RrPt/REM/Gehaeuse/REM-M/REM-M-Unterteil_V2.0.stl

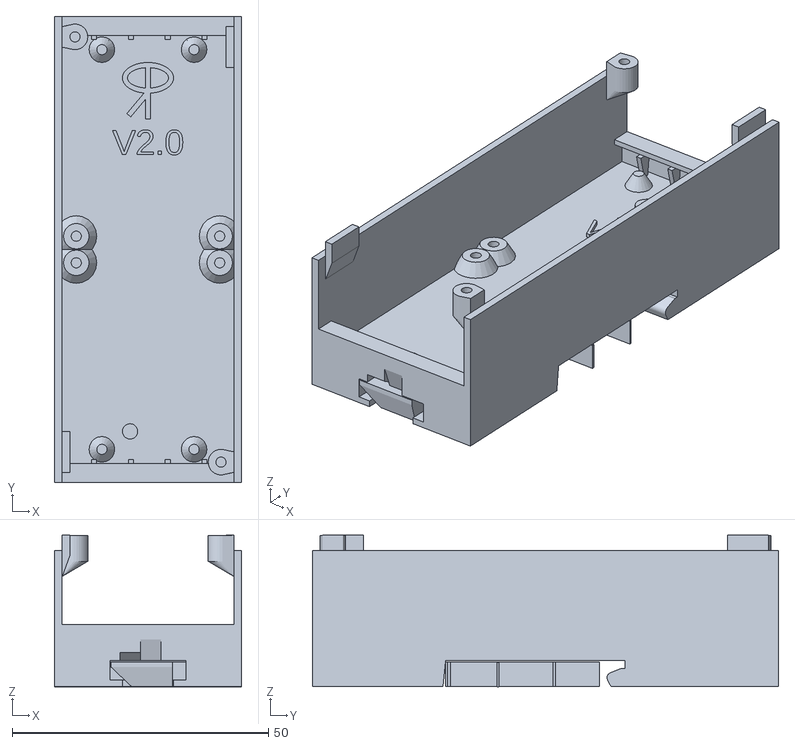
[picture p20: CAD file, 2020-09-23]
Gehaeuse/REM-M/REM-M-Unterteil_V2.0.stl
36.5 x 91.0 x 29.6
