RrPt/REM/REM-Platinen/3d/Lolin32.FCStd

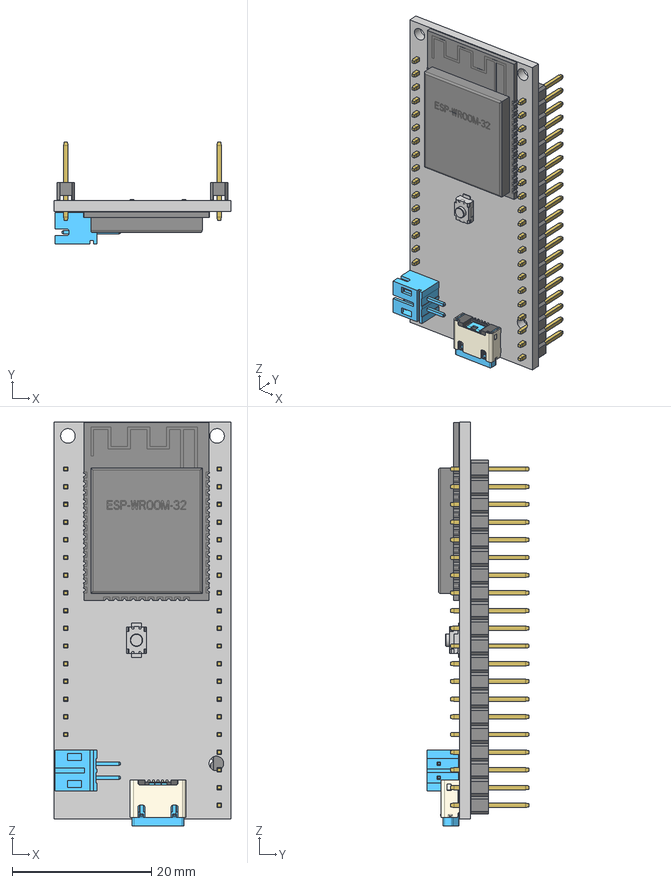
[picture p21: CAD file, 2020-09-23]
REM-Platinen/3d/Lolin32.FCStd
25.4 x 14.6 x 58.0 mm
W\X\FCrth 629105150521 Micro USB (Housing)
W\X\FCrth 629105150521 Micro USB (Inner Shield)
W\X\FCrth 629105150521 Micro USB (Outer Shield)
W\X\FCrth 629105150521 Micro USB ( Contact 1,2,4,5)
W\X\FCrth 629105150521 Micro USB ( Contact 1,2,4,5)001
W\X\FCrth 629105150521 Micro USB ( Contact 1,2,4,5)002
W\X\FCrth 629105150521 Micro USB ( Contact 1,2,4,5)003
W\X\FCrth 629105150521 Micro USB ( Contact 3)
B2B-PH-K-S v1
BASE, 2
PIN, 2
PIN, 003
PIN, 004
PIN, 005
PIN, 006
PIN, 007
PIN, 008
PIN, 009
PIN, 010
PIN, 011
PIN, 012
PIN, 013
PIN, 014
PIN, 015
PIN, 016
PIN, 017
BASE, 003
PIN, 018
PIN, 019
PIN, 020
PIN, 021
PIN, 022
PIN, 023
PIN, 024
PIN, 025
PIN, 026
PIN, 027
PIN, 028
PIN, 029
PIN, 030
PIN, 031
PIN, 032
PIN, 033
ESP-WROOM-32
3x4x2 tact button v1
BASE, 004
PIN, 039
PIN, 036
PIN, 041
PIN, 042
PIN, 038
PIN, 037
PIN, 047
PIN, 043
PIN, 048
PIN, 044
PIN, 040
PIN, 045
PIN, 046
PIN, 049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
