RrPt/REM/REM-Platinen/Platinen/modules/3dpackages/LED_D3.0mm_long.step

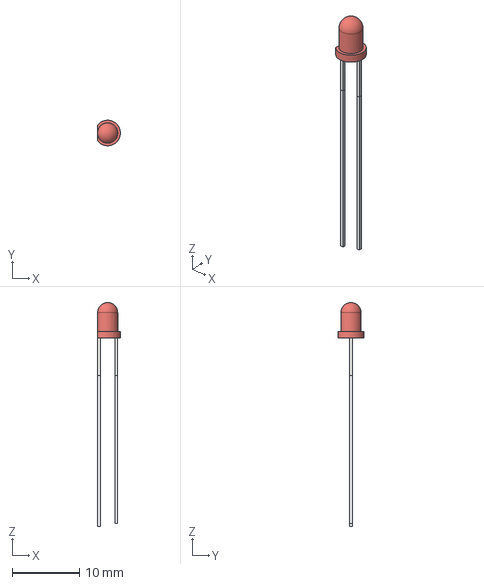
[picture p22: CAD file, 2020-09-23]
REM-Platinen/Platinen/modules/3dpackages/LED_D3.0mm_long.step
3.40 x 3.80 x 33.2 mm
