RrPt/REM/Gehaeuse/REM-M/REM-M-Klammer_V1.2.stl

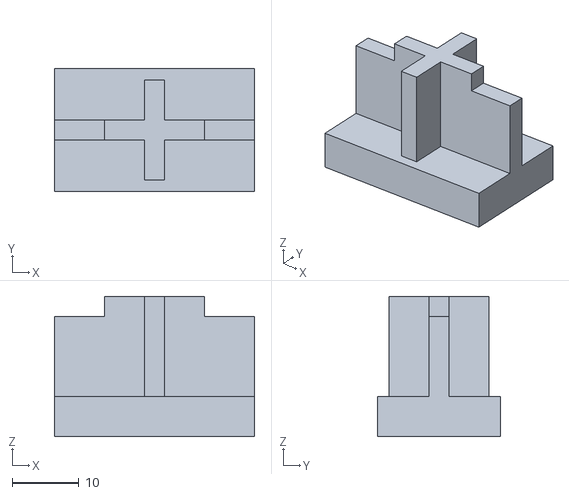
[picture p23: CAD file, 2020-09-23]
Gehaeuse/REM-M/REM-M-Klammer_V1.2.stl
30.0 x 18.5 x 21.0
