RrPt/REM/REM-Platinen/Platinen/modules/3dpackages/PinHeader_2x05_P2.54mm_Vertical_mit_Stecker.step

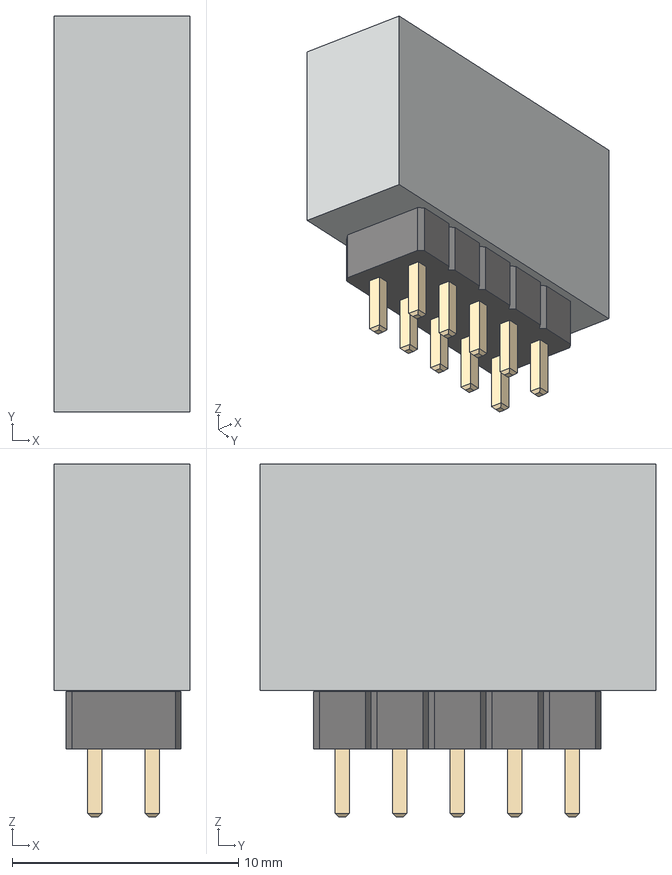
[picture p24: CAD file, 2020-09-23]
REM-Platinen/Platinen/modules/3dpackages/PinHeader_2x05_P2.54mm_Vertical_mit_Stecker.step
6.00 x 17.5 x 15.6 mm
