RrPt/REM/REM-Platinen/Platinen/modules/3dpackages/MicroButton2.step

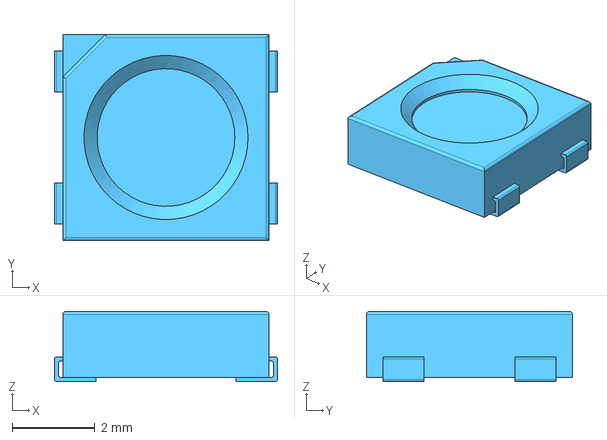
[picture p25: CAD file, 2020-09-23]
REM-Platinen/Platinen/modules/3dpackages/MicroButton2.step
5.40 x 5.00 x 1.70 mm
