RrPt/REM/REM-Platinen/Platinen/modules/3dpackages/pxc_1726189_05_MKKDSN-1-5-6-5-08_3D.stp

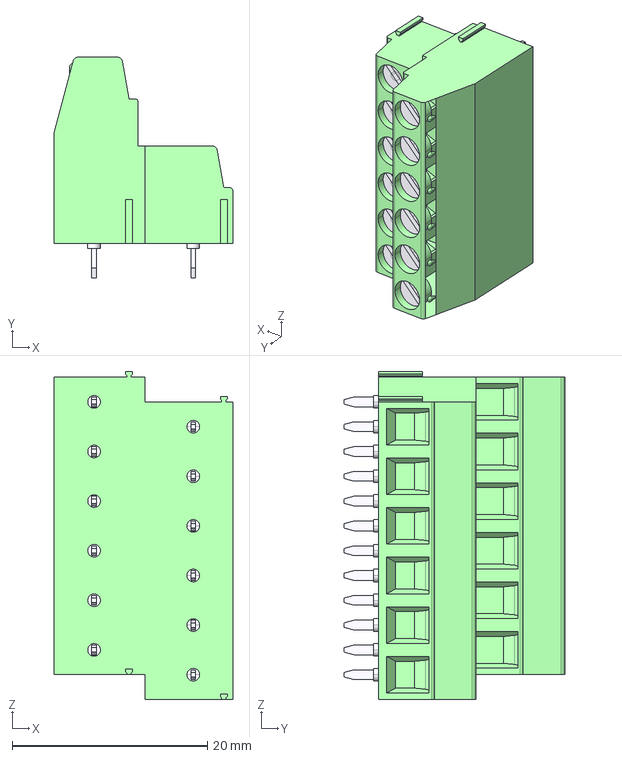
[picture p26: CAD file, 2020-09-23]
REM-Platinen/Platinen/modules/3dpackages/pxc_1726189_05_MKKDSN-1-5-6-5-08_3D.stp
18.3 x 22.6 x 33.6 mm
